kjanderson/MIDI-Router/06-verification/PR-003 - SW - USB CDC lockup.docx

Problem Report PR-002

HW part: HW0001, HW0002

HW rev: HW0001 R002, HW0002 R001

Description: Using CDC application results in device lockup.

Steps to recreate the problem:

1. Activate character echo application in app.c (echo each received byte to emulated serial port output)
2. Wait 3 sec
3. Verify MODE LED continues to blink

Test result: Fail

Resolution: TBD.
