kjanderson/MIDI-Router/06-verification/PR-001 - PCB - Mode LED.docx

Problem Report PR-001

HW part: HW0001

HW rev: R002

Description: PCB hardware is not able to drive the MODE LED.

Steps to recreate the problem:

1. Apply +5V to 5V input
2. Verify 1.2V appears at 1.2V rail
3. Verify 3.3V appears at 3.3V rail
4. Verify MODE LED illuminates

Test result: Fail (given procedure fails at step 4)

Resolution: Mode function from IC1 pin 33 to IC1 pin 32.
