kjanderson/MIDI-Router/05-implementation/02-code/01-mcu/fpga_image.c

#include <stdint.h>
#include "fpga_image.h"

const uint8_t vuFpgaImage[FPGA_IMAGE_SIZE] =
{
  0xFF, 0x00, 0x4C, 0x61, 0x74, 0x74, 0x69, 0x63, 
  0x65, 0x00, 0x69, 0x43, 0x45, 0x63, 0x75, 0x62, 
  0x65, 0x32, 0x20, 0x32, 0x30, 0x32, 0x30, 0x2E, 
  0x31, 0x32, 0x2E, 0x32, 0x37, 0x39, 0x34, 0x33, 
  0x00, 0x50, 0x61, 0x72, 0x74, 0x3A, 0x20, 0x69, 
  0x43, 0x45, 0x34, 0x30, 0x48, 0x58, 0x31, 0x4B, 
  0x2D, 0x56, 0x51, 0x31, 0x30, 0x30, 0x00, 0x44, 
  0x61, 0x74, 0x65, 0x3A, 0x20, 0x53, 0x65, 0x70, 
  0x20, 0x34, 0x20, 0x32, 0x30, 0x32, 0x31, 0x20, 
  0x30, 0x35, 0x3A, 0x30, 0x34, 0x3A, 0x00, 0xFF, 
  0x34, 0x38, 0x00, 0x7E, 0xAA, 0x99, 0x7E, 0x51, 
  0x00, 0x01, 0x05, 0x92, 0x00, 0x20, 0x62, 0x01, 
  0x4B, 0x72, 0x00, 0x90, 0x82, 0x00, 0x00, 0x11, 
  0x00, 0x01, 0x01, 0x00, 0x00, 0x00, 0x00, 0x00, 
  0x00, 0x00, 0x00, 0x00, 0x08, 0x00, 0x00, 0x00, 
  0x00, 0x00, 0x00, 0x20, 0x00, 0x00, 0x00, 0x00, 
  0x00, 0x00, 0x00, 0x00, 0x00, 0x00, 0x00, 0x00, 
  0x00, 0x00, 0x00, 0x00, 0x00, 0x00, 0x00, 0x00, 
  0x00, 0x00, 0x00, 0x00, 0x00, 0x00, 0x00, 0x00, 
  0x00, 0x00, 0x00, 0x00, 0x00, 0x00, 0x00, 0x00, 
  0x00, 0x00, 0x00, 0x00, 0x00, 0x00, 0x00, 0x00, 
  0x00, 0x00, 0x00, 0x00, 0x00, 0x00, 0x00, 0x00, 
  0x00, 0x00, 0x00, 0x00, 0x00, 0x00, 0x00, 0x00, 
  0x00, 0x00, 0x00, 0x00, 0x00, 0x00, 0x00, 0x00, 
  0x00, 0x00, 0x00, 0x00, 0x00, 0x00, 0x00, 0x04, 
  0x00, 0x00, 0x00, 0x00, 0x00, 0x00, 0x10, 0x00, 
  0x00, 0x00, 0x00, 0x00, 0x00, 0x00, 0x00, 0x00, 
  0x00, 0x00, 0x00, 0x00, 0x00, 0x00, 0x00, 0x00, 
  0x00, 0x40, 0x00, 0x00, 0x00, 0x00, 0x00, 0x00, 
  0x00, 0x00, 0x00, 0x00, 0x00, 0x00, 0x00, 0x00, 
  0x00, 0x00, 0x00, 0x00, 0x00, 0x00, 0x00, 0x00, 
  0x00, 0x00, 0x00, 0x00, 0x00, 0x00, 0x00, 0x00, 
  0x00, 0x00, 0x00, 0x00, 0x00, 0x00, 0x00, 0x00, 
  0x00, 0x00, 0x00, 0x00, 0x00, 0x00, 0x00, 0x00, 
  0x00, 0x00, 0x00, 0x00, 0x00, 0x00, 0x00, 0x00, 
  0x00, 0x00, 0x08, 0x00, 0x00, 0x00, 0x20, 0x00, 
  0x00, 0x20, 0x00, 0x00, 0x00, 0x80, 0x00, 0x00, 
  0x00, 0x00, 0x00, 0x00, 0x00, 0x00, 0x00, 0x00, 
  0x00, 0x00, 0x00, 0x00, 0x00, 0x00, 0x00, 0x00, 
  0x00, 0x00, 0x00, 0x00, 0x00, 0x00, 0x00, 0x00, 
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
};
