kjanderson/MIDI-Router/05-implementation/02-code/01-mcu/usb-app/app_device_cdc_to_uart.c

/*******************************************************************************
Copyright 2016 Microchip Technology Inc. (www.microchip.com)

Licensed under the Apache License, Version 2.0 (the "License");
you may not use this file except in compliance with the License.
You may obtain a copy of the License at

    http://www.apache.org/licenses/LICENSE-2.0

Unless required by applicable law or agreed to in writing, software
distributed under the License is distributed on an "AS IS" BASIS,
WITHOUT WARRANTIES OR CONDITIONS OF ANY KIND, either express or implied.
See the License for the specific language governing permissions and
limitations under the License.

To request to license the code under the MLA license (www.microchip.com/mla_license), 
please contact mla_licensing@microchip.com
*******************************************************************************/

/** INCLUDES *******************************************************/
#include "system.h"

#include <stdint.h>
#include <string.h>
#include <stddef.h>

#include "usb.h"

#include "app_led_usb_status.h"
#include "app_device_cdc_to_uart.h"
#include "usb_config.h"
//#include "usart.h"

#define mDataRdyUSART() 1U
#define mTxRdyUSART() 1U

/** VARIABLES ******************************************************/

//static bool buttonPressed;
//static char buttonMessage[] = "Button pressed.\r\n";
static uint8_t USB_Out_Buffer[CDC_DATA_OUT_EP_SIZE];
static uint8_t RS232_Out_Data[CDC_DATA_IN_EP_SIZE];

unsigned char  NextUSBOut;
unsigned char    NextUSBOut;
unsigned char    LastRS232Out;  // Number of characters in the buffer
unsigned char    RS232cp;       // current position within the buffer
unsigned char RS232_Out_Data_Rdy = 0;
USB_HANDLE  lastTransmission;


/*********************************************************************
* Function: void APP_DeviceCDCEmulatorInitialize(void);
*
* Overview: Initializes the demo code
*
* PreCondition: None
*
* Input: None
*
* Output: None
*
********************************************************************/
void APP_DeviceCDCEmulatorInitialize()
{
    uint8_t i;
    
    CDCInitEP();
    
    line_coding.bCharFormat = 0;
    line_coding.bDataBits = 8;
    line_coding.bParityType = 0;
    line_coding.dwDTERate = 19200;
    
    // Initialize the arrays
    for (i=0; i<sizeof(USB_Out_Buffer); i++)
    {
        USB_Out_Buffer[i] = 0;
    }
    
    NextUSBOut = 0;
    LastRS232Out = 0;
    lastTransmission = 0;
}

/*********************************************************************
* Function: void APP_DeviceCDCEmulatorTasks(void);
*
* Overview: Keeps the demo running.
*
* PreCondition: The demo should have been initialized and started via
*   the APP_DeviceCDCEmulatorInitialize() and APP_DeviceCDCEmulatorStart() demos
*   respectively.
*
* Input: None
*
* Output: None
*
********************************************************************/
void APP_DeviceCDCEmulatorTasks()
{
    /* If the USB device isn't configured yet, we can't really do anything
     * else since we don't have a host to talk to.  So jump back to the
     * top of the while loop. */
    if( USBGetDeviceState() < CONFIGURED_STATE )
    {
        return;
    }

    /* If we are currently suspended, then we need to see if we need to
     * issue a remote wakeup.  In either case, we shouldn't process any
     * keyboard commands since we aren't currently communicating to the host
     * thus just continue back to the start of the while loop. */
    if( USBIsDeviceSuspended()== true )
    {
        return;
    }

    if (RS232_Out_Data_Rdy == 0)  // only check for new USB buffer if the old RS232 buffer is
    {						  // empty.  This will cause additional USB packets to be NAK'd
        LastRS232Out = getsUSBUSART(RS232_Out_Data,64); //until the buffer is free.
        if(LastRS232Out > 0)
        {
            RS232_Out_Data_Rdy = 1;  // signal buffer full
            RS232cp = 0;  // Reset the current position
        }
    }

    //Check if one or more bytes are waiting in the physical UART transmit
    //queue.  If so, send it out the UART TX pin.
    if(RS232_Out_Data_Rdy)
    {
#if defined(USB_CDC_SUPPORT_HARDWARE_FLOW_CONTROL)
        //Make sure the receiving UART device is ready to receive data before
        //actually sending it.
        if(UART_CTS == USB_CDC_CTS_ACTIVE_LEVEL)
        {
            USART_putcUSART(RS232_Out_Data[RS232cp]);
            ++RS232cp;
            if (RS232cp == LastRS232Out) {
                RS232_Out_Data_Rdy = 0;
            }
        }
#else
        //Hardware flow control not being used.  Just send the data.
        if ((NextUSBOut < CDC_DATA_OUT_EP_SIZE) &&
                (RS232cp < CDC_DATA_IN_EP_SIZE)) {
            USB_Out_Buffer[NextUSBOut] = RS232_Out_Data[RS232cp];
        }
        NextUSBOut++;
        RS232cp++;
        if (RS232cp == LastRS232Out) {
            RS232_Out_Data_Rdy = 0;
        }
#endif
    }

    //Check if we received a character over the physical UART, and we need
    //to buffer it up for eventual transmission to the USB host.
#if 0
    if(NextUSBOut < (CDC_DATA_OUT_EP_SIZE - 1))
    {
        //USB_Out_Buffer[NextUSBOut] = USART_getcUSART();
        //++NextUSBOut;
        USB_Out_Buffer[NextUSBOut] = 0;
    }
#endif

#if defined(USB_CDC_SUPPORT_HARDWARE_FLOW_CONTROL)
    //Drive RTS pin, to let UART device attached know if it is allowed to
    //send more data or not.  If the receive buffer is almost full, we
    //deassert RTS.
    if(NextUSBOut <= (CDC_DATA_OUT_EP_SIZE - 5u))
    {
        UART_RTS = USB_CDC_RTS_ACTIVE_LEVEL;
    }
    else
    {
            UART_RTS = (USB_CDC_RTS_ACTIVE_LEVEL ^ 1);
    }
#endif

    //Check if any bytes are waiting in the queue to send to the USB host.
    //If any bytes are waiting, and the endpoint is available, prepare to
    //send the USB packet to the host.
    if((USBUSARTIsTxTrfReady()) && (NextUSBOut > 0))
    {
        putUSBUSART(&USB_Out_Buffer[0], NextUSBOut);
        NextUSBOut = 0;
    }

    CDCTxService();
}
